Cap-n-Proud/Bailey/hardware/Img/1-818-2-original.jpg

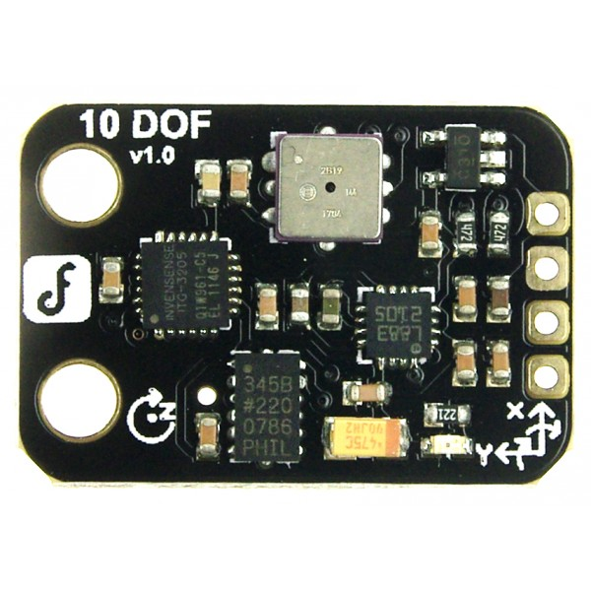
hardware/Img/1-818-2-original.jpg
