Cap-n-Proud/Bailey/hardware/Img/51xSlxCabZL._SL500_AA300_.jpg

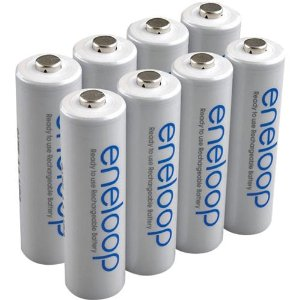
hardware/Img/51xSlxCabZL._SL500_AA300_.jpg
