Cap-n-Proud/Bailey/hardware/Img/im130731002_3.jpg

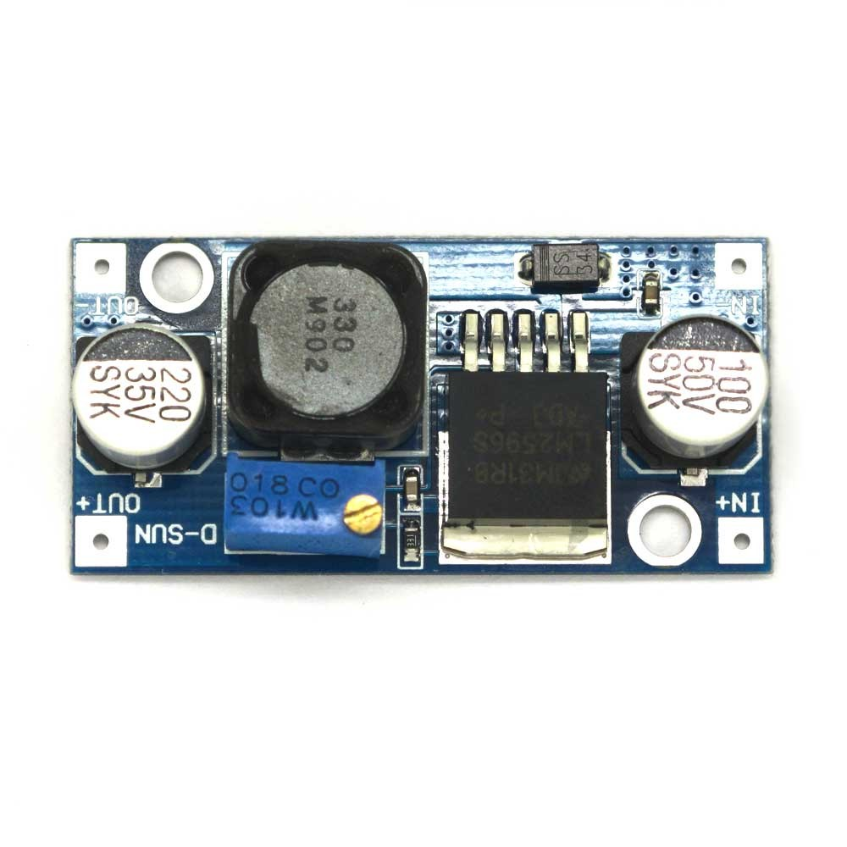
hardware/Img/im130731002_3.jpg
