Cap-n-Proud/Bailey/hardware/Img/pololu-12v-100-1-gear-motor-encoder.jpg

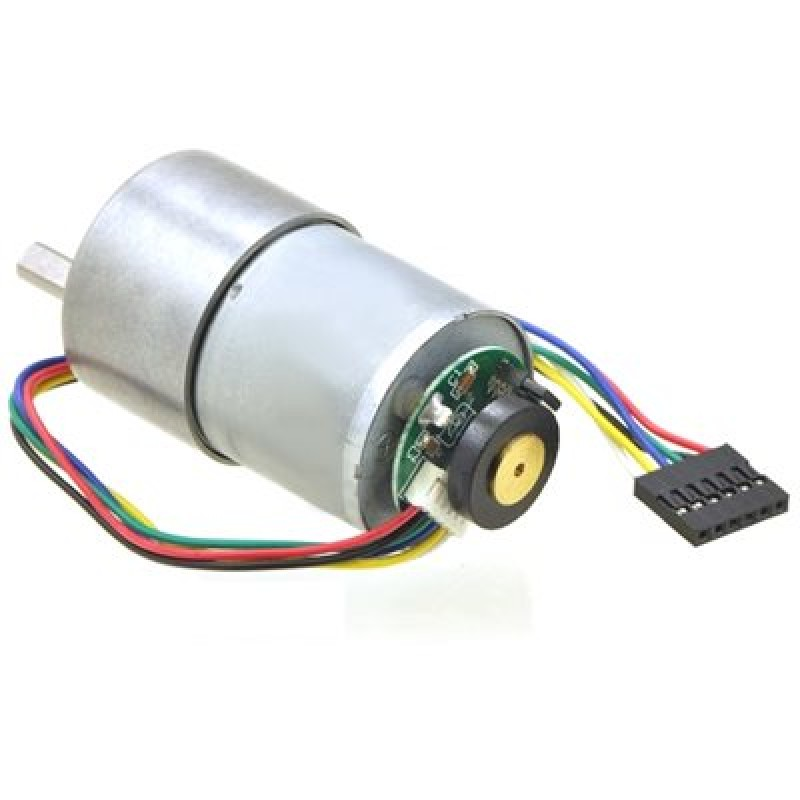
hardware/Img/pololu-12v-100-1-gear-motor-encoder.jpg
